MartinDavidWaller/D70Box/Pictures/IMG_0920.JPG

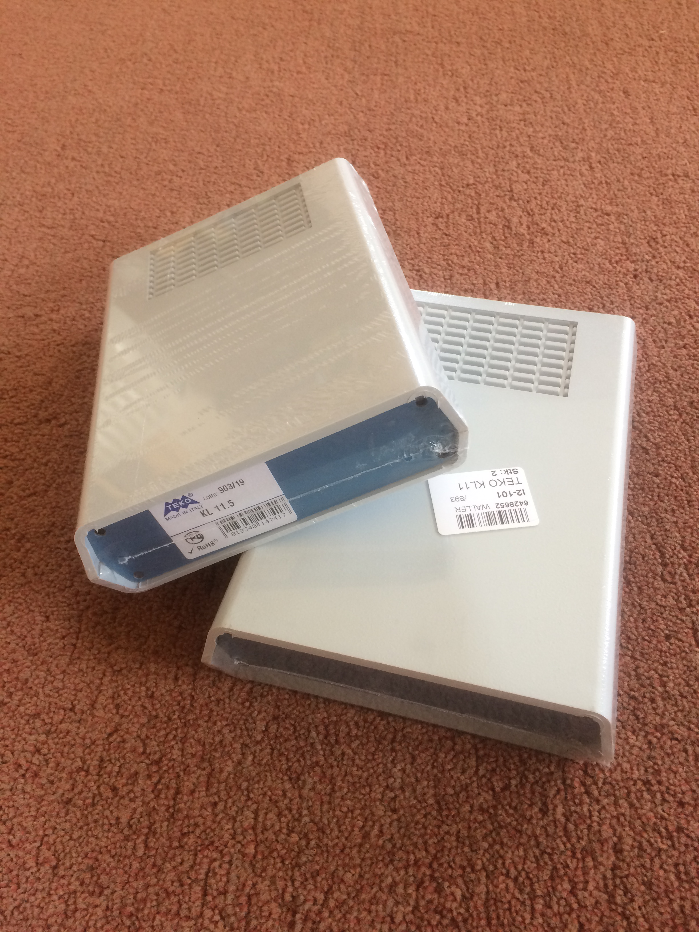
Pictures/IMG_0920.JPG
