MartinDavidWaller/D70Box/Pictures/IMG_0935.jpg

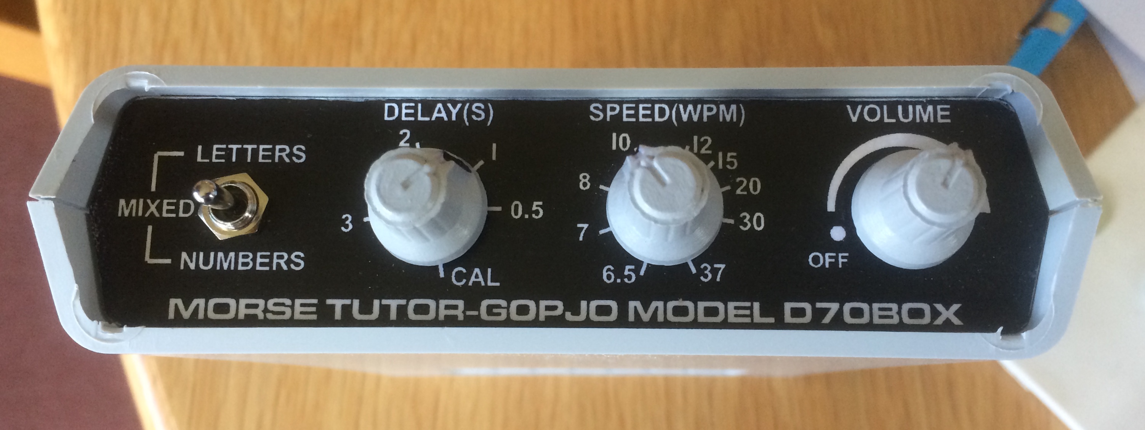
Pictures/IMG_0935.jpg
